jmstark/lazyLegoCar/Fotos/IMG_1472.JPG

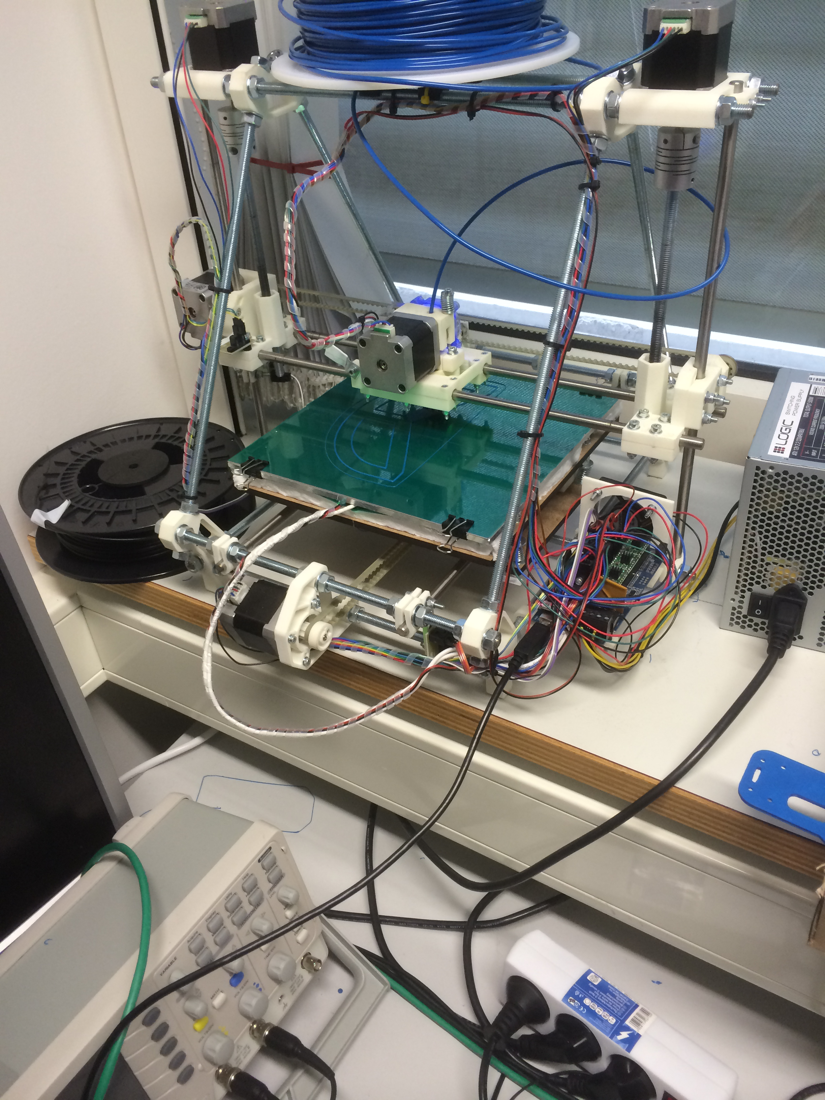
Fotos/IMG_1472.JPG
