jmstark/lazyLegoCar/Fotos/IMG_1473.JPG

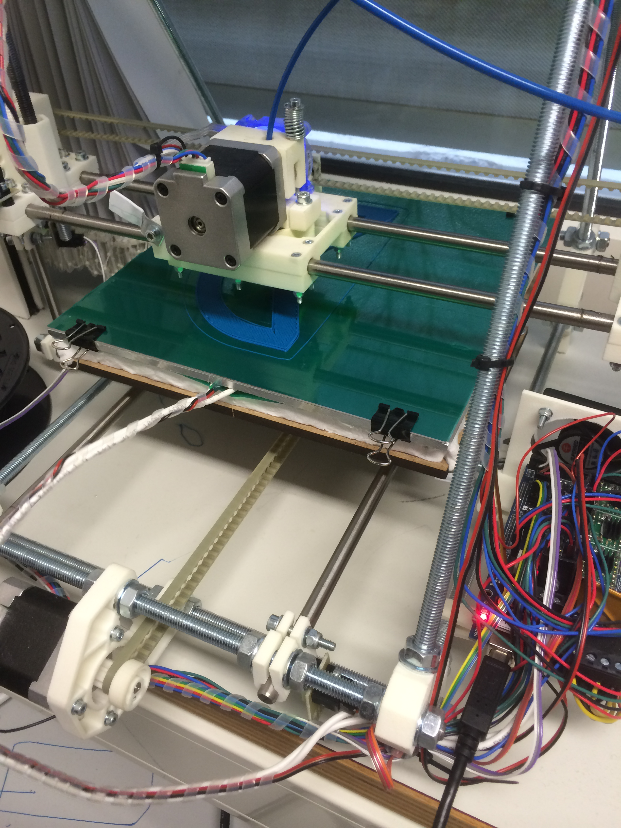
Fotos/IMG_1473.JPG
