jmstark/lazyLegoCar/Fotos/IMG_1474.JPG

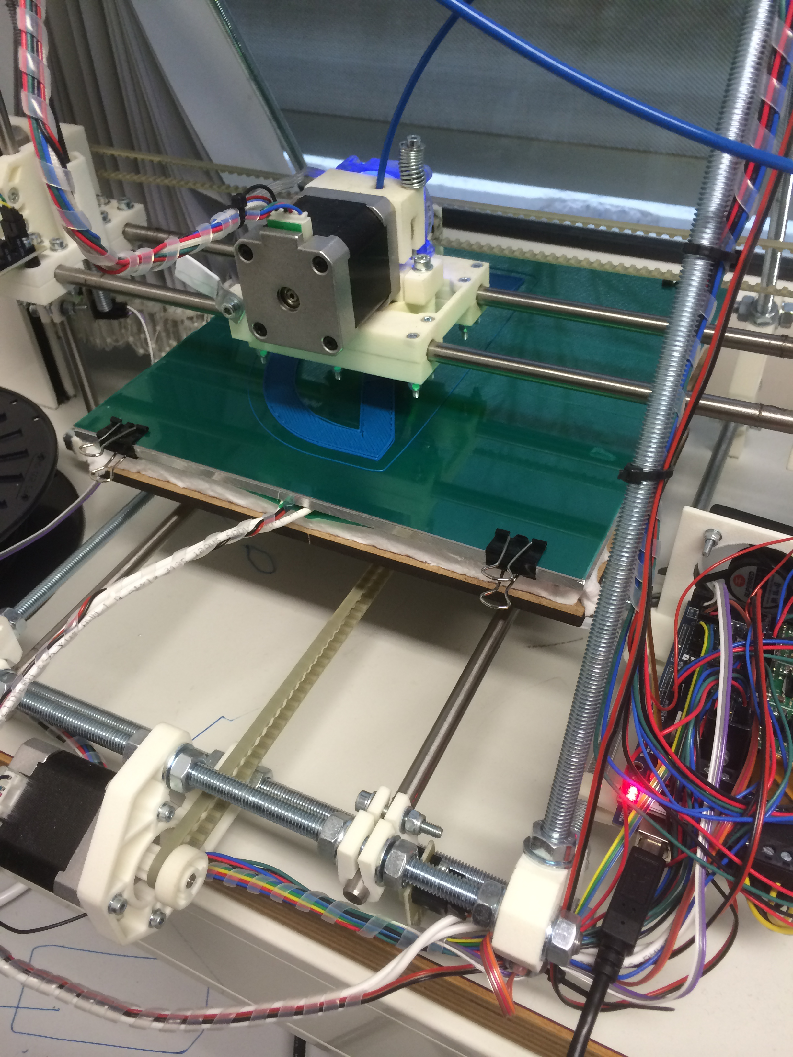
Fotos/IMG_1474.JPG
