jmstark/lazyLegoCar/raspberry/threads.cpp

#include "threads.h"

void socketThreadEntry(rasp_sock::RaspberrySocket *sPtr, comSync *cPtr, Observer* o){
	std::string str, command, value;
	int x,y;
	//std::thread *t;
	if(sPtr == NULL || cPtr == NULL){
		fprintf(stderr, "invalid sock-thread args\n");
		return;
	}
	
//reinitialize_sock:
//	sPtr->initSocket();
wait_for_client:
    o->controlYellowLed(false);
	sPtr->waitForClient();
	o->controlYellowLed(true);
	while(1){
		if(sPtr->isConnected() == 0){
			printf("client disconnected\n");
			goto wait_for_client;
		}
		str = sPtr->receive();
		std::cout<<str<<std::endl;
		if(str.compare(COMMAND_FWD) == 0){
			o->drive(DIR_FWD);
			/*cPtr->mtx.lock();
			cPtr->comc.direction = 1;
			cPtr->mtx.unlock();
			cPtr->changed.store(true, std::memory_order_relaxed);*/
		}
		else if(str.compare(COMMAND_RWD) == 0){
			o->drive(DIR_RWD);
			/*cPtr->mtx.lock();
			cPtr->comc.direction = -1;
			cPtr->mtx.unlock();
			cPtr->changed.store(true, std::memory_order_relaxed);*/
		}
		else if(str.compare(COMMAND_LEFT) == 0){
			o->steer(LEFT);
			/*cPtr->mtx.lock();
			cPtr->comc.steering = -1;
			cPtr->mtx.unlock();
			cPtr->changed.store(true, std::memory_order_relaxed);*/
		}
		else if(str.compare(COMMAND_RIGHT) == 0){
			o->steer(RIGHT);
			/*cPtr->mtx.lock();
			cPtr->comc.steering = 1;
			cPtr->mtx.unlock();
			cPtr->changed.store(true, std::memory_order_relaxed);*/
		}
		else if(str.compare(COMMAND_STRAIGHT) == 0){
			o->steer(STRAIGHT);
			/*cPtr->mtx.lock();
			cPtr->comc.steering = 0;
			cPtr->mtx.unlock();
			cPtr->changed.store(true, std::memory_order_relaxed);*/
		}
		else if(str.compare(COMMAND_STOP) == 0){
			o->drive(DIR_STOP);
			/*cPtr->mtx.lock();
			cPtr->comc.direction = 0;
			cPtr->mtx.unlock();
			cPtr->changed.store(true, std::memory_order_relaxed);*/
		}
		size_t blank = str.find_first_of(' ');
		command = str.substr(0, blank);
		value = str.substr(blank+1, std::string::npos);
		std::cout << "command: " << command << "\tvalue: " << value << std::endl;
		if(command.compare(COMMAND_DESTINATION) == 0){
			sscanf(value.c_str(), "%d %d", &x, &y);
#ifdef RASP_DEBUG
			printf("received new destination: %d|%d\n", x, y);
			//std::thread t(pathFindingThread, o, x, y);
			o->toArduino.x = x;
			o->toArduino.y = y;
			o->toArduino.pathFinding = true;
#endif
		}
		else if(command.compare(COMMAND_SPEED) == 0){
			cPtr->mtx.lock();
			cPtr->comc.speed = std::stoi(value);
			cPtr->mtx.unlock();
			cPtr->changed.store(true, std::memory_order_relaxed);
			printf("received new Speed: %d\n", std::stoi(value));
		}
		/* old speed-setting
		else if(1==0){
			cPtr->mtx.lock();
			cPtr->comc.speed = std::stoi(str);
			cPtr->mtx.unlock();
			cPtr->changed.store(true, std::memory_order_relaxed);
		}
		*/
	}
}


void pathFindingThread(Observer *obs){
pf_loop:
	while(obs->toArduino.pathFinding == false){
		sleep(5);
	}
	obs->controlRedLed(true);
	printf("path-finding-thread startet\n\tdriving to (%d,%d)\n", obs->toArduino.x, obs->toArduino.y);
	Path path(obs->toArduino.x,obs->toArduino.y,&obs->toArduino, obs);
	path.drive();
	obs->toArduino.pathFinding = false;
	obs->controlRedLed(false);
	goto pf_loop;
}
