jmstark/lazyLegoCar/raspberry/socket.h

#pragma once
#ifndef RASP_SOCK
#define RASP_SOCK
#ifndef LEGO_STD_PORT
#define LEGO_STD_PORT 4359
#endif
#ifndef BUF_LEN
#define BUF_LEN 512
#endif
#include "stdafx.h"

namespace rasp_sock{
	class RaspberrySocket{
		public:
			RaspberrySocket();
			~RaspberrySocket();
			bool initSocket();
			bool waitForClient();
			std::string receive();
			int sendMsg(const std::string&);
			void cleanup(bool flag = false);
			int isConnected(){return c_socket;}
			
		private:
			int s_socket, c_socket;
			struct sockaddr_in server, client;
	};
};

#endif
